jankrejci/njordr/pcb/components/packages/D-SOD-323.step

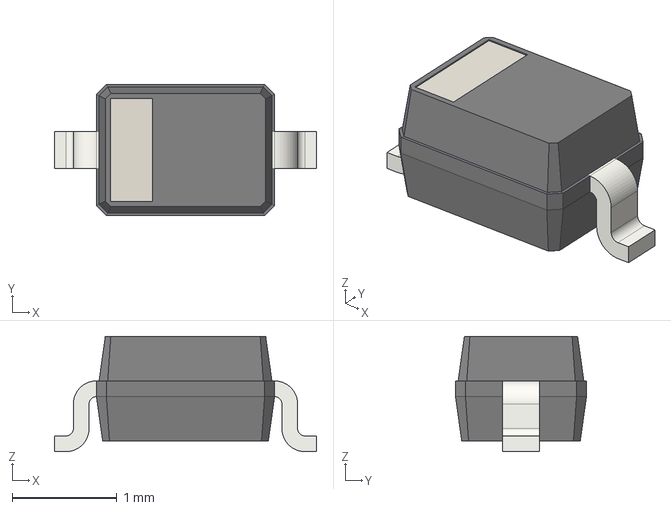
[picture p15: CAD file, 2025-10-25]
pcb/components/packages/D-SOD-323.step
2.50 x 1.25 x 1.10 mm
