jankrejci/njordr/pcb/components/packages/R-0603.step

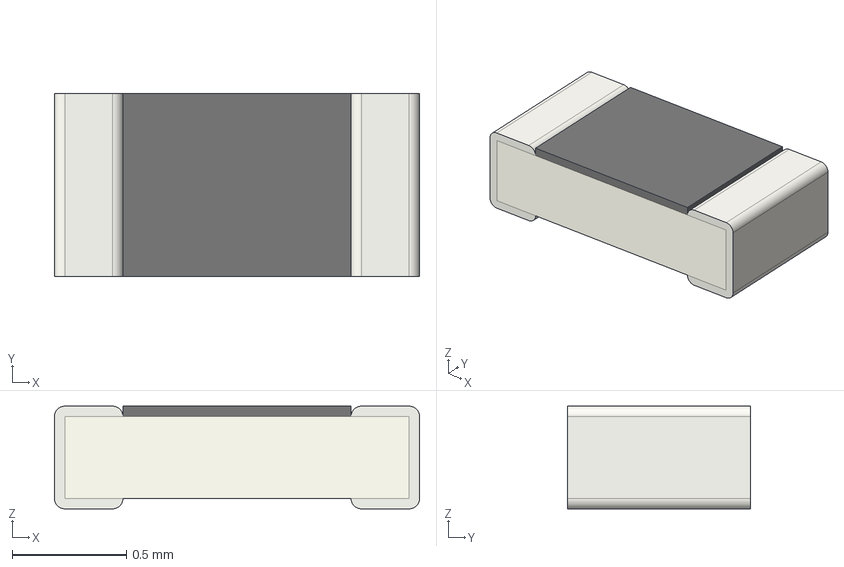
[picture p16: CAD file, 2025-10-25]
pcb/components/packages/R-0603.step
1.60 x 0.8 x 0.45 mm
