jankrejci/njordr/pcb/components/packages/SOT-23-6.step

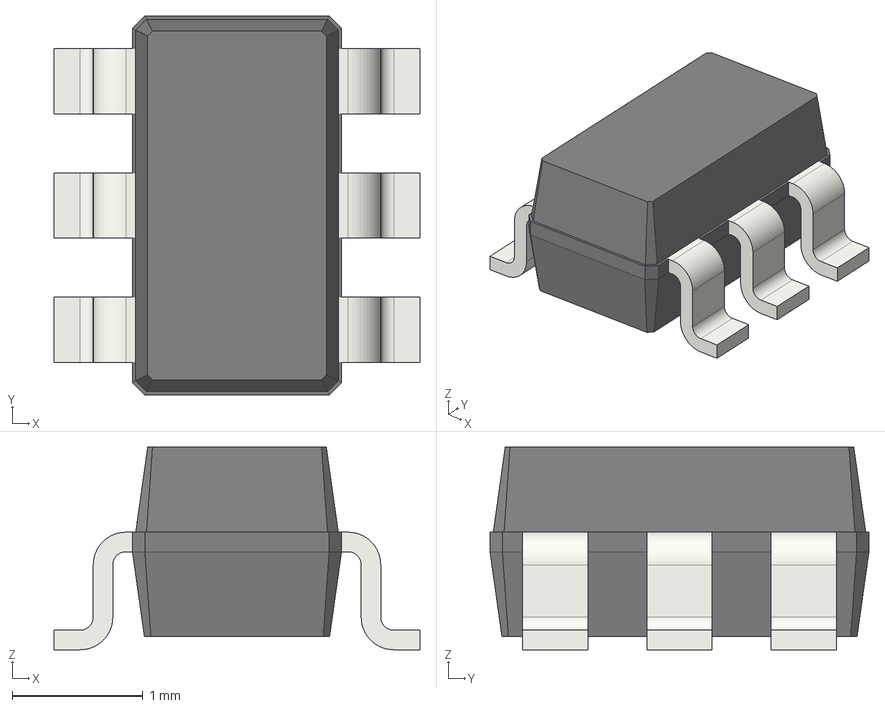
[picture p17: CAD file, 2025-10-25]
pcb/components/packages/SOT-23-6.step
2.80 x 2.90 x 1.55 mm
