jankrejci/njordr/pcb/components/packages/L-Axial-L7.0-D3.3-P10.16.step

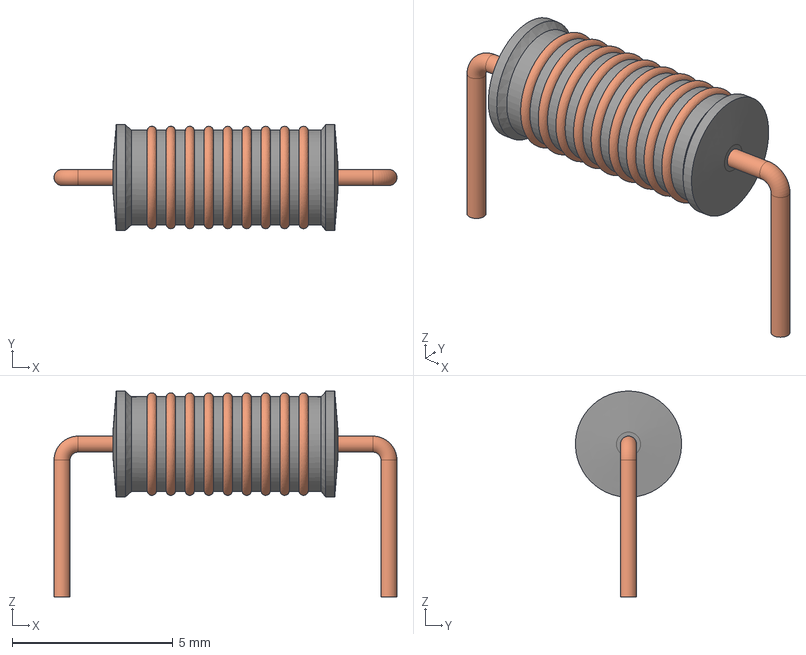
[picture p18: CAD file, 2025-10-25]
pcb/components/packages/L-Axial-L7.0-D3.3-P10.16.step
10.7 x 3.30 x 6.40 mm
