jankrejci/njordr/pcb/components/packages/C-1206.step

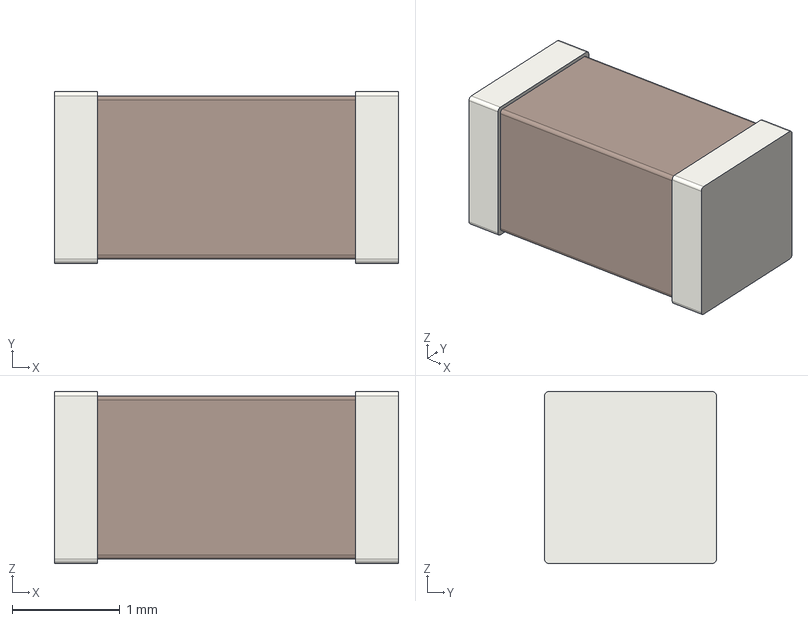
[picture p19: CAD file, 2025-10-25]
pcb/components/packages/C-1206.step
3.20 x 1.60 x 1.60 mm
