jankrejci/njordr/pcb/components/packages/TSSOP-20-4.4x6.5.step

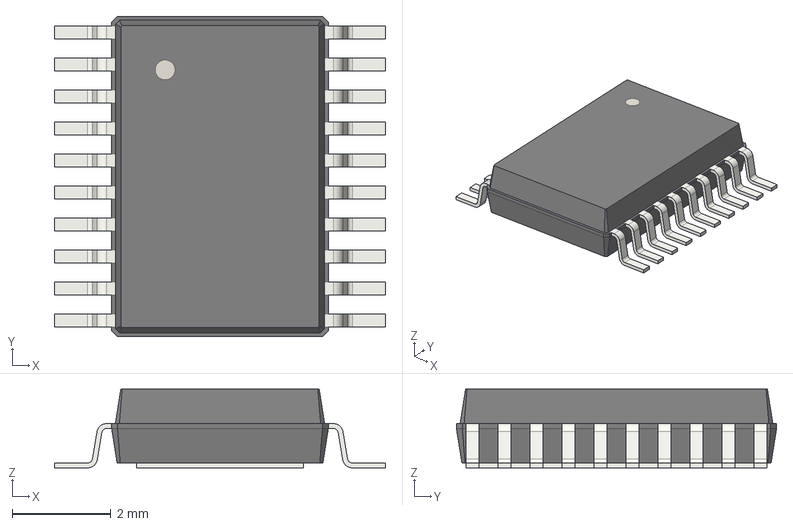
[picture p20: CAD file, 2025-10-25]
pcb/components/packages/TSSOP-20-4.4x6.5.step
6.72 x 6.50 x 1.60 mm
