jankrejci/njordr/pcb/components/packages/L-Axial-L12.0-D5.0-P15.24.step

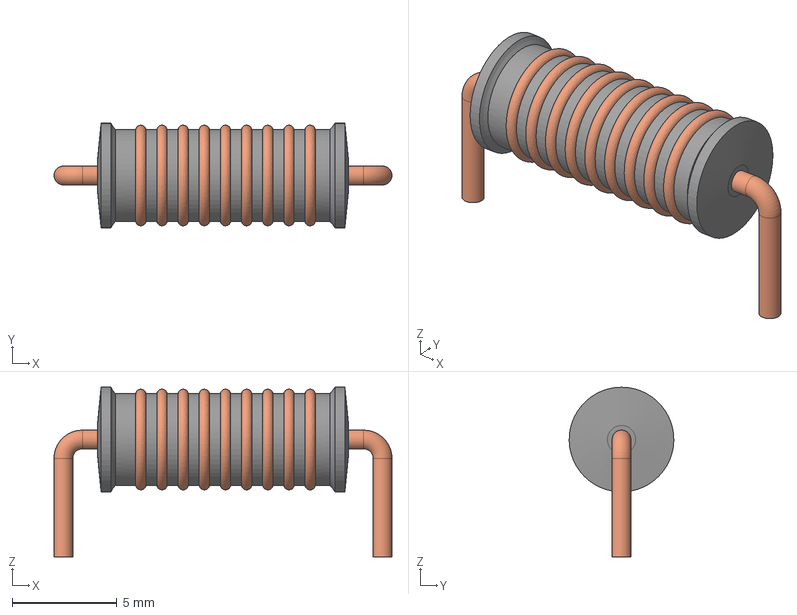
[picture p21: CAD file, 2025-10-25]
pcb/components/packages/L-Axial-L12.0-D5.0-P15.24.step
16.1 x 5.00 x 8.10 mm
